szbergeron/yahp/sampler/src/sampler2.cpp

#include "config.cpp"
#include "utils.cpp"

#include "ADC.h"
#include "ADC_Module.h"
#include "core_pins.h"

#ifndef YAHP_SAMPLER
#define YAHP_SAMPLER

// it seems that a typical conversion takes about 4.92-ish
// microseconds when set to averaging(0) and the fastest
// conversion speed
//
// this gives us ~29000 cycles at stock clocks,
// which should give us some good compute during idle!
// it also means we get about 49 microseconds per
// sample of even a 20 key range (if we aren't split
// across boards weirdly, and can run both adcs at
// full saturation), meaning 20 samples per millisecond
// of even a "pretty severe" load scenario across
// all "READY" keys therein
static const uint32_t CONVERSION_TIME_NS = 49000;

__attribute__((always_inline)) static inline void step_idle(uint32_t window_ns,
                                                            bool run_all);

struct sample_t {

  float height;
  uint32_t time;

  sample_t(float height, uint32_t time) : height(height), time(time) {}

  sample_t() : height(0), time(0) {}
};

template <uint32_t BUFSIZE = SAMPLE_BUFFER_LENGTH> struct sample_buf_t {
  sample_t buffer[BUFSIZE];

  // begin points at the newest sample,
  // and (begin + 1) % SAMPLE_BUFFER_LENGTH is the next newest
  uint32_t begin = 0;
  uint32_t size = 0;

  uint32_t unackd = 0;

  sample_buf_t() : begin(0), size(0), unackd(0) {}

  void add_sample(sample_t sample) {
    /*this->begin =
        (this->begin + SAMPLE_BUFFER_LENGTH - 1) % SAMPLE_BUFFER_LENGTH;*/
    this->begin++;
    this->begin %= BUFSIZE;

    this->unackd += 1;

    this->buffer[this->begin] = sample;
    if (this->size < BUFSIZE) {
      this->size++;
    }
  }

  void clear() {
    this->begin = 0;
    this->size = 0;
    this->unackd = 0;
  }

  // if n is greater than buffer length,
  // then the oldest still held sample is returned
  // if no samples exist, the sample will be "zero"
  sample_t read_nth_oldest(uint32_t n) {
    // Serial.println("N is: " + String(n));
    //  clamp n
    if (n > BUFSIZE) [[unlikely]] {
      n = BUFSIZE;
    }

    auto res = sample_t{0, 0};
    if (this->size == 0) {
      // keep default
    } else {
      auto start = this->begin;
      auto with_room = start + BUFSIZE;
      auto offsetted = with_room - n;
      auto idx = offsetted % BUFSIZE;
      // Serial.println("Returns idx: " + String(idx));
      res = this->buffer[idx];
    }

    return res;
  }

  inline sample_t latest() { return this->read_nth_oldest(0); }
};

struct sensor_t;

struct sample_request_t {
  sensor_t *sensor;
  uint8_t pin;

  sample_request_t() : sensor(nullptr), pin(0) {}

  // if this was default constructed, this will return false
  bool is_real() { return this->sensor != nullptr; }

  sample_request_t(uint8_t pin, sensor_t *sensor) : sensor(sensor), pin(pin) {}
};

struct sensor_t {
  enum class sensor_mode_e {
    KEY,
    PEDAL,
    FADER,
  };

  enum class poll_priority_e {
    SLOW, // the slowest of the bunch, means
          // we can poll "rarely" in computer timescales
          // indicates events that want to happen within
          // "window of present" at human timescales,
          // but is not
    RELAXED,
    CRITICAL,
  };

  uint32_t sensor_id = 0;

  sample_buf_t<SAMPLE_BUFFER_LENGTH> buf;
  poll_priority_e priority = poll_priority_e::RELAXED;
  interpolater_t<MAGNET_INTERPOLATOR_POINTS> curve;

  uint8_t pin = 0;

  // key should be immediately sampled
  bool due_now() {
    uint32_t now = micros();

    switch (this->priority) {
    case poll_priority_e::SLOW:
      // TODO
      return true;
    case poll_priority_e::RELAXED:
      if (now - this->buf.latest().time > MAX_STALENESS_MICROS) {
        return true;
      } else {
        return false;
      }
    case poll_priority_e::CRITICAL:
      return true; // AFAP, but why are you asking me?
    default:
      [[unlikely]] return false;
    }
  }

  // key should be sampled _if convenient_
  bool due_relaxed() {
    uint32_t now = micros();

    if (now - this->buf.latest().time > MIN_STALENESS_MICROS) {
      return true;
    } else {
      return false;
    }
  }

  sample_request_t make_sample_request() {
    return sample_request_t(this->pin, this);
  }

  void add_raw_sample(uint32_t time, uint16_t raw_value) {
    auto nv = this->curve.interpolate(raw_value);
    this->buf.add_sample(sample_t(nv, time));
  }

  sensor_t(uint8_t pin, uint32_t sensor_id,
           vector_t<point_t, MAGNET_INTERPOLATOR_POINTS> curve)
      : sensor_id(sensor_id), curve(curve), pin(pin) {
    //
  }

  /*sensor_t(): curve(0, 1000) {
    // errorln("sensor_t was default constructed");
  }*/
};

struct adc_info_t {
  bool allowed_pins[PIN_COUNT];
  ADC_Module *adcm;

  adc_info_t(int idx, ADC *adc)
      : allowed_pins{}, adcm(idx == 0 ? adc->adc0 : adc->adc1) {
    for (int i = 0; i < KEYS_PER_BOARD; i++) {
      auto pin = pins[i];
      auto allowed = adcm->checkPin(pin);
      this->allowed_pins[pin] = allowed;
    }
  }

  adc_info_t() : allowed_pins{}, adcm(nullptr) {}
};

struct adcs_info_t {
  ADC *adcp;
  adc_info_t adc[2];

  adcs_info_t(ADC *adcp)
      : adcp(adcp), adc{adc_info_t(0, adcp), adc_info_t(1, adcp)} {}

  adcs_info_t() : adc{} {}
};

struct board_t {
  vector_t<sensor_t, KEYS_PER_BOARD> keys;
  uint8_t board_num;
  adcs_info_t adcs;

  void do_round() {
    // check if we even need to sample anything
    bool some_due = false;

    for (auto &k : this->keys) {
      if (k.due_now()) {
        some_due = true;
      }
    }

    if (!some_due) {
      // move on asap
      return;
    } else {
      // set board now so we have time for sample
      set_board(this->board_num);
      delayMicroseconds(1);
    }

    // start setting the pins _now_
    // so we have as much time as possible
    // before needing to sample

    vector_t<sample_request_t, KEYS_PER_BOARD> requests;

    for (auto &k : this->keys) {
      if (k.due_now() || k.due_relaxed()) {
        auto r = k.make_sample_request();
        requests.push_back(r);
      }
    }

    this->sample_all(requests);
  }

  void sample_all(vector_t<sample_request_t, KEYS_PER_BOARD> &requests) {
    vector_t<sample_request_t, KEYS_PER_BOARD> for_a;
    vector_t<sample_request_t, KEYS_PER_BOARD> for_b;
    vector_t<sample_request_t, KEYS_PER_BOARD> for_both;

    for (auto request : requests) {
      bool allowed_0i = this->adcs.adc[0].allowed_pins[request.pin];
      bool allowed_1i = this->adcs.adc[1].allowed_pins[request.pin];

      if (allowed_0i && allowed_1i) {
        // allowed for both, can't yet assign greedily
        for_both.push_back(request);
      } else if (allowed_0i) {
        // exclusively allowed for adc0, so can greedily push
        for_a.push_back(request);
      } else if (allowed_1i) {
        // same for adc1
        for_b.push_back(request);
      } else {
        // ???
        errorln("an assigned pin wasn't valid on either adc for sampling");
      }
    }

    sample_request_t a;
    sample_request_t b;

    while (!for_a.empty() || !for_b.empty() || !for_both.empty()) {
      if (!for_a.empty()) {
        a = for_a.pop_back().unwrap();
      } else if (!for_both.empty()) {
        a = for_both.pop_back().unwrap();
      }

      if (!for_b.empty()) {
        b = for_b.pop_back().unwrap();
      } else if (!for_both.empty()) {
        b = for_both.pop_back().unwrap();
      }

      uint32_t ts_a;
      uint32_t ts_b;

      auto &adc_a = this->adcs.adc[0].adcm;
      auto &adc_b = this->adcs.adc[1].adcm;

#undef FASTREAD
#ifdef FASTREAD
      if (a.is_real()) {
#ifdef YAHP_DEBUG
        bool v = adc_a->checkPin(a.pin);
        if (!v) {
          eloop(String("adc 0 (a) tried to read disallowed pin: ") + a.pin);
        }
#endif
        adc_a->startReadFast(a.pin);
        ts_a = micros();
        ;
      }

      if (b.is_real()) {
#ifdef YAHP_DEBUG
        bool v = adc_b->checkPin(b.pin);
        if (!v) {
          eloop(String("adc 1 (b) tried to read disallowed pin: ") + b.pin);
        }
#endif
        adc_b->startReadFast(b.pin);
        ts_b = micros();
        ;
      }

      // do one big-budget run
      step_idle(CONVERSION_TIME_NS, false);

      while (true) {
        bool a_done = true;
        bool b_done = true;

        // is either one done?
        if (a.is_real() && !adc_a->isComplete()) {
          a_done = false;
        }
        if (b.is_real() && !adc_b->isComplete()) {
          b_done = false;
        }

        // track when _both_ are complete
        // so that we avoid having to do individual stalls below,
        // should reduce code size in this loop
        if (a_done && b_done) {
          break;
        }

        // if not, at the moment we want to avoid
        // too much complexity and the gains from calling
        // step_once _again_ with so little time remaining
        // would probably be negligible
      }

      // get values
      if (a.is_real()) {
        auto v_a = adc_a->readSingle();
        sample_t s(v_a, ts_a);
        a.sensor->add_sample(s);
      }

      if (b.is_real()) {
        auto v_b = adc_b->readSingle();
        sample_t s(v_b, ts_b);
        a.sensor->add_sample(s);
      }
#elif defined(FASTREAD2)
      //
#else
      // Serial.println("Adding round");
      if (a.is_real() && b.is_real()) {
        ts_a = micros();
        ts_b = micros();

        auto r = this->adcs.adcp->analogSynchronizedRead(a.pin, b.pin);
        auto v_a = r.result_adc0;
        auto v_b = r.result_adc1;
        /*adc_a->startSingleRead(a.pin);
        adc_b->startSingleRead(b.pin);

        step_idle(CONVERSION_TIME_NS, false);

        auto v_a = adc_a->readSingle();
        auto v_b = adc_b->readSingle();*/
        sample_t sa(v_a, ts_a);
        sample_t sb(v_b, ts_b);

        a.sensor->add_raw_sample(ts_a, v_a);
        b.sensor->add_raw_sample(ts_b, v_b);

      } else if (a.is_real()) {

        ts_a = micros();
        auto v_a = adc_a->analogRead(a.pin);

        a.sensor->add_raw_sample(ts_a, v_a);

      } else if (b.is_real()) {

        ts_b = micros();
        auto v_b = adc_b->analogRead(b.pin);

        b.sensor->add_raw_sample(ts_b, v_b);
      }

#endif
    }
  }

  board_t(boardspec_t &bspec, adcs_info_t &adcs_info)
      : board_num(bspec.board_num), adcs(adcs_info) {
    for (auto &keyc : bspec.sensors) {
      Serial.printf("Creates sensor by id %d\r\n", keyc.sensor_id);
      sensor_t sensor(keyc.pin_num, keyc.sensor_id, keyc.curve);
      this->keys.push_back(sensor);
    }
  }
};

struct sampler_t {
  ADC *adc = nullptr;
  vector_t<board_t, NUM_BOARDS> boards;

  sensor_t *find_sensor(uint32_t sensor_id) {
    for (auto &board : this->boards) {
      for (auto &sensor : board.keys) {
        if (sensor.sensor_id == sensor_id) {
          return &sensor;
        }
      }
    }
    Serial.printf("Unable to find sensor by id %d?\r\n", sensor_id);
    for (auto &board : this->boards) {
      Serial.printf("Board by id %d:\r\n", (int)board.board_num);
      for (auto &sensor : board.keys) {
        Serial.printf("    Sensor by id %d\r\n", sensor.sensor_id);
      }
    }

    return nullptr;
  }

  sampler_t(ADC adc_, samplerspec_t &spec) : adc(new ADC(adc_)) {
    for (auto boardc : spec.boards) {
      adcs_info_t info(this->adc);
      Serial.printf("Makes board: %d\r\n", (int)boardc.board_num);
      board_t b(boardc, info);
      this->boards.push_back(b);
    }
  }

  ~sampler_t() { delete this->adc; }

  void sample_round() {
    set_board_pins();
    delayMicroseconds(10);
    for (auto &board : this->boards) {
      board.do_round();
    }
  }
};

#endif
