szbergeron/yahp/sampler/src/calibrate.cpp

#include "avr/pgmspace.h"
#include "config.cpp"
#include "key.cpp"
#include "keyboard.cpp"
#include "magnets.cpp"
#include "pins_arduino.h"
#include "usb_serial.h"
#include "utils.cpp"

#include "ArduinoJson/Document/JsonDocument.hpp"
#include "ArduinoJson/Object/JsonObject.hpp"

#include "core_pins.h"
#include "elapsedMillis.h"
#include <cstddef>
#include <cstdint>
#include <ostream>

#ifndef YAHP_CALIBRATE
#define YAHP_CALIBRATE
void blinkblink() {
  for (int i = 0; i < 3; i++) {
    digitalWrite(LED_BUILTIN, 1);
    delay(150);
    digitalWrite(LED_BUILTIN, 0);
    delay(250);
  }
}

void testmode(tempboards_t &boards) {
  while (true) {
    Serial.println("1) fast toggle with numeric output");
    Serial.println("2) toggle board on enter");
    auto num = prompt_int("make choice:", 1, 3, 0);
    if (num == 1) {
      while (!newline_waiting()) {
        for (auto &board : boards.boards) {
          Serial.printf("\r\nSetting to board %d\r\n", (uint32_t)board);
          set_board(board);
          delayMicroseconds(50);

          for (uint32_t ipin = 0; ipin < KEYS_PER_BOARD; ipin++) {
            uint32_t val = analogRead(pins[ipin]);
            Serial.printf("%04d ", val);
          }
          Serial.printf("\r\n");
        }

        delay(100);
      }
    } else if (num == 2) {
      while (true) {
        for (auto &board : boards.boards) {
          Serial.printf("\r\nSetting to board %d\r\n", (uint32_t)board);
          set_board(board);
          delayMicroseconds(50);

          while (!newline_waiting()) {
            for (uint32_t ipin = 0; ipin < KEYS_PER_BOARD; ipin++) {
              uint32_t val = analogRead(pins[ipin]);
              Serial.printf("%04d ", val);
            }
            Serial.printf("\r");
          }
        }

        delay(100);
      }
    }
  }
}

tempboards_t detect_boards() {
  Serial.println("Getting board info");
  // const size_t LINE_LEN = 256;
  // uint8_t linebuf[LINE_LEN];

  // first, detect which boards are present
  // do this by checking if we can pull up/down
  // the voltage on the lines, or if
  // they automatically return to some given value
  // // for now, just ask \:)
  Serial.print("How many boards are there? [0-255]:");

  uint8_t board_count = prompt_int("How many boards are there?", 0, 255, 1);

  Serial.printf("Setting to %d boards\n\r", board_count);

  vector_t<uint8_t, NUM_BOARDS> boards;

  bool sequential = false;

  sequential =
      confirm("Are they numbered sequentially starting from zero?", true);

  Serial.println();

  if (sequential) {
    for (size_t i = 0; i < board_count; i++) {
      boards.push_back(i);
    }
  } else {
    for (size_t i = 0; i < board_count; i++) {
      uint8_t bid = prompt_int(String("What is the board ID of board number ") +
                                   String(i) + "?",
                               0, 255, i);

      boards.push_back(bid);
    }
  }

  return {boards};
}

vector_t<vector_t<bool, KEYS_PER_BOARD>, NUM_BOARDS>
detect_keys(tempboards_t &boards) {

  for (size_t i = 0; i < KEYS_PER_BOARD; i++) {
    pinMode(pins[i], INPUT_PULLDOWN);
  }

  analogReadResolution(10);

  analogReadAveraging(16);

  Serial.println("Detecting keys on boards, using voltage threshold of 0.1v as "
                 "'grounded'");

  float vp = 0.1 / 3.3;
  float thres_f = vp * 1024;
  uint32_t thres = thres_f;

  vector_t<vector_t<bool, KEYS_PER_BOARD>, NUM_BOARDS> info;

  for (auto &bid : boards.boards) {
    set_board(bid);
    delayMicroseconds(100);

    vector_t<bool, KEYS_PER_BOARD> bi;

    for (size_t i = 0; i < KEYS_PER_BOARD; i++) {
      delayMicroseconds(30);
      uint32_t val = analogRead(pins[i]);

      if (val > thres) {
        bi.push_back(true);
      } else {
        bi.push_back(false);
      }
    }

    info.push_back(bi);
  }

  Serial.println("Discovered sensor configuration:");

  for (size_t b = 0; b < info.size(); b++) {
    auto &bd = info[b];

    Serial.printf("  (%d)[", b);

    for (size_t s = 0; s < bd.size(); s++) {
      auto present = bd[s];

      if (present) {
        Serial.print("X");
      } else {
        Serial.print("_");
      }
    }

    Serial.print("]");
  }

  for (size_t b = 0; b < info.size(); b++) {
    Serial.printf("b# %d has %d\r\n", b, info[b].size());
  }

  Serial.println();

  return info;
}

float gather_gbl_val(String msg, key_calibration_t &kc, sensorspec_t &ssp) {
  Serial.println(msg);
  Serial.println();
  float latest = 0;
  while (true) {
    if (newline_waiting()) {
      break;
    }

    auto v = analogRead(ssp.pin_num);
    float normal = kc.map(v);

    Serial.print("\r");
    for (int i = 0; i < 12; i++) {
      Serial.print("          ");
    }
    Serial.print("\r");
    print_normalized(normal);
    latest = normal;
    delay(30);
  }

  float val = prompt_float(msg, 0, 1, latest);
  Serial.printf("You selected %f\r\n", val);
  bool c = confirm("do you want to continue with this val?", true);
  if (c) {
    return val;
  } else {
    return gather_gbl_val(msg, kc, ssp);
  }
}

global_key_config_t gbl_config(keyboardspec_t &spec) {
  Serial.println("making global");
  sensorspec_t *sensor = nullptr;
  boardspec_t *board = nullptr;
  key_spec_t *key = nullptr;
  // just pick a key
  for (auto &board_i : spec.sampler.boards) {
    board = &board_i;
    for (auto &sensor_i : board_i.sensors) {
      sensor = &sensor_i;
      goto OUT;
    }
  }
OUT:

  if (sensor == nullptr) {
    Serial.println("No keys were found!");
    return global_key_config_t();
  }

  for (auto &key_i : spec.keys) {
    if (key_i.sensor_id == sensor->sensor_id) {
      key = &key_i;
    }
  }

  if (key == nullptr) {
    Serial.println("No keys were found!");
    return global_key_config_t();
  }

  // now, figure out detect range
  auto kc = key_calibration_t(*key, *sensor);

  set_board(board->board_num);
  delay(3);

  global_key_config_t gbl;

  gbl.strike =
      gather_gbl_val("What strike point do you want to use?", kc, *sensor);
  gbl.letoff =
      gather_gbl_val("What letoff point do you want to use?", kc, *sensor);
  gbl.repetition =
      gather_gbl_val("What repetition point do you want to use?", kc, *sensor);
  gbl.active =
      gather_gbl_val("What active point do you want to use?", kc, *sensor);
  gbl.damper_down =
      gather_gbl_val("What damper_down point do you want to use?", kc, *sensor);
  gbl.damper_up =
      gather_gbl_val("What damper_up point do you want to use?", kc, *sensor);

  return gbl;
}

tempkey_t select_key(tempboards_t &boards) {
  analogReadResolution(10);
  analogReadAveraging(16);

  uint32_t baselines[NUM_BOARDS][KEYS_PER_BOARD];
  for (size_t b = 0; b < NUM_BOARDS; b++) {
    for (size_t k = 0; k < KEYS_PER_BOARD; k++) {
      baselines[b][k] = 0x9FFF;
    }
  }

  delayMicroseconds(100);

  for (size_t b = 0; b < boards.boards.size(); b++) {
    auto bnum = boards.boards[b];
    set_board(bnum);
    delayMicroseconds(100);

    for (size_t knum = 0; knum < KEYS_PER_BOARD; knum++) {
      auto pin = pins[knum];
      baselines[b][knum] = analogRead(pin);
    }
  }

  Serial.println("Please press the key you want to select");

  while (true) {
    for (size_t b = 0; b < boards.boards.size(); b++) {
      auto bnum = boards.boards[b];
      set_board(bnum);
      delayMicroseconds(100);

      for (size_t knum = 0; knum < KEYS_PER_BOARD; knum++) {
        auto pin = pins[knum];
        uint32_t baseline = baselines[b][knum];
        uint16_t val = analogRead(pin);
        if (val > baseline + 75) {
          for (int i = 0; i < 16; i++) {
            if ((uint32_t)analogRead(pin) < baseline + 75) {
              Serial.printf("had a spurious spike, static?");
              goto OUT;
            }
          }
          Serial.printf("baseline was %d, val found was %d, on bnum %d pin %d, "
                        "pin_index %d\r\n",
                        (int)baseline, (int)val, (int)bnum, (int)pin,
                        (int)knum);
          return tempkey_t(bnum, pin);
        }
      OUT:
        continue;
      }
    }
  }
}

void testmode_entry() {
  auto boards = detect_boards();
  testmode(boards);
}

keyboardspec_t key_calibration2() {
    while (!newline_waiting()) {
      delay(500);
      Serial.println("Press enter to continue");
    }

    auto boards = detect_boards();

    uint32_t start_midi =
        prompt_int("What is the lowest midi note on your piano? (Usually the "
                   "minimum on an 88 key keyboard is 21)",
                   0, 127, FIRST_MIDI_NOTE + 30);
        uint32_t midi_channel = prompt_int(
            "What midi channel should notes play on by default?", 0, 16, 1);

    Serial.printf("Please play each key, one at a time, ascending from 0");
    Serial.printf("When done, hit enter");

    vector_t<tempkey_t, KEY_COUNT_MAX> ided_sensors;

    vector_t<key_spec_t, KEY_COUNT_MAX> kspecs;
    vector_t<boardspec_t, KEY_COUNT_MAX> bspecs;

    size_t sensor_id = 0;

    while(!newline_waiting()) {
        auto k = select_key(boards);
        if(ided_sensors.contains(k)) {
            continue;
        }

        ided_sensors.push_back(k);

        auto sid = sensor_id++;
        auto mnid = start_midi++;
        sensorspec_t(sid, k.pin, {});
        key_spec_t(sid, mnid, midi_channel);

        auto bn = k.board;

        auto b = bspecs.find_by_or_insert([bn](const boardspec_t &b) { return bn == b.board_num; }, boardspec_t());

    }

}

void more_calibration(fullspec_t fspec) {
}

keyboardspec_t key_calibration() {
  while (!newline_waiting()) {
    delay(500);
    Serial.println("Press enter to continue");
  }

  auto boards = detect_boards();

  if (confirm("enter test mode?", false)) {
    testmode(boards);
  }

  bool fastcal = confirm("Do you want to use fastcal?", true);

  samplerspec_t samplerspec;
  vector_t<key_spec_t, KEY_COUNT_MAX> keys;
  vector_t<pedal_spec_t, PEDAL_COUNT_MAX> pedals;

  uint32_t start_midi =
      prompt_int("What is the lowest midi note on your piano? (Usually the "
                 "minimum on an 88 key keyboard is 21)",
                 0, 127, FIRST_MIDI_NOTE + 30);

  uint32_t midi_channel = prompt_int(
      "What midi channel should notes play on by default?", 0, 16, 1);

  uint32_t num_keys =
      prompt_int("How many keys does your piano have?", 0, 127 - start_midi,
                 min(88, 127 - (int32_t)start_midi));

  uint32_t csid = 0;
  for (uint32_t midi_num = start_midi; midi_num < start_midi + num_keys;
       midi_num++) {
    auto n = format_note(midi_num);
    Serial.printf("Configuring note %s (midi id %d)\r\n", n.c_str(),
                  (int)midi_num);
    bool in_use = fastcal || confirm("Configure this key?", true);
    if (!in_use) {
      continue;
    }

    Serial.printf("Please press %s on your piano (will be sid %d)\r\n",
                  n.c_str(), csid);
    auto sensor = select_key(boards);

    //

    Serial.printf("Key %s is assigned pin %d on board %d\r\n", n.c_str(),
                  (int)sensor.pin, (int)sensor.board);

    auto interpolater = drop_test(sensor.board, sensor.pin, fastcal);

    uint32_t sid = csid++;

    sensorspec_t sensorspec(sid, sensor.pin, interpolater.points);

    samplerspec.get_board(sensor.board).sensors.push_back(sensorspec);
    key_spec_t k(sid, midi_num, midi_channel);
    keys.push_back(k);
  }

  while (confirm("Do you have an additional pedal to add?", false)) {
    Serial.println("Not implemented");
  }

  return keyboardspec_t(samplerspec, keys, pedals);
}

float read_key(uint32_t sid, keyboard_t *kbd) {
  return kbd->sampler->find_sensor(sid)->buf.latest().height;
}

// Doesn't free itself, reboot after done!
keyboard_t *make_kbd(fullspec_t spec) {
  ADC adc;
  auto sampler = new sampler_t(adc, spec.keyboard.sampler);
  auto kbd = new keyboard_t(spec, sampler);

  return kbd;
}

JsonDocument configure_offsets(fullspec_t &spec) {
  auto kbd = make_kbd(spec);

  confirm("Hands off the keyboard! Hit enter once understood", true);
  delay(500);

  const uint32_t AVERAGES_COUNT = 500;

  for (uint32_t averages = 0; averages < AVERAGES_COUNT; averages++) {
    /*for (auto &key : spec.keyboard.keys) {
        //
    }*/
    //
    kbd->sampler->sample_round();
    for (kbd_key_t &key : kbd->keys) {
      float cur_val = read_key(key.sensor->sensor_id, kbd);

      if (averages == 0) {
        key.calibration.spec.bound_min = cur_val;
        key.calibration.spec.bound_max = cur_val;
      } else {
        key.calibration.spec.bound_min =
            (key.calibration.spec.bound_min * averages + cur_val) /
            (averages + 1);
      }
    }
  }

  Serial.println("Now, play each note at PPP level (or lift the hammer just "
                 "barely to touch the striker rail!)");
  Serial.println("Press enter when done");

  while (!newline_waiting()) {
    kbd->sampler->sample_round();
    for (kbd_key_t &key : kbd->keys) {
      float cur_val = read_key(key.sensor->sensor_id, kbd);

      key.calibration.spec.bound_max =
          max(key.calibration.spec.bound_max, cur_val);
    }
  }

  if (confirm("Do you want to use the new range config generated here?",
              true)) {
    JsonDocument jd;
    for (kbd_key_t &key : kbd->keys) {
      JsonDocument jdi;

      jdi["min"] = key.calibration.spec.bound_min;
      jdi["max"] = key.calibration.spec.bound_max;

      jd[key.sensor->sensor_id] = jdi;
      //
    }

    return jd;
  } else {
    // just reboot
    doReboot();
    JsonDocument never;
    return never;
  }
}

const size_t JSON_FILE_MAX_LENGTH = 250000;
DMAMEM char JSON_FILE[JSON_FILE_MAX_LENGTH];

result_t<JsonDocument *, unit_t> json_from_sd(const char *name) {
  Serial.println("Grabbing json from sd");

  if (!SD.exists(name)) {
    Serial.println("No config on SD");
    return result_t<JsonDocument *, unit_t>::err({});
  }

  auto f = SD.open(name, FILE_READ);

  size_t file_size = 0;

  file_size = f.readBytes((char*)JSON_FILE, JSON_FILE_MAX_LENGTH);

  JSON_FILE[file_size] = 0; // null term

  f.close();

  Serial.println("done loading file");

  JsonDocument *doc = new JsonDocument;
  deserializeJson(*doc, (char*)JSON_FILE);

  Serial.println("deserialized");

  return result_t<JsonDocument *, unit_t>::ok(doc);
}

void json_to_sd(const char *name, JsonDocument doc) {
  Serial.println("Saving config to sd...");
  auto f = SD.open(name, FILE_WRITE_BEGIN);
  size_t len = serializeJsonPretty(doc, f);
  f.flush();
  f.close();
}

static fullspec_t get_spec() {
  keyboardspec_t s;
  {
    auto r = json_from_sd("calibration.json");
    if (r.is_ok()) {
      auto d = r.unwrap();
      Serial.println("Loaded calibration json file");
      // we already have sampler then
      s = keyboardspec_t((*d).as<JsonObject>());
      delete d;
    } else {
      s = key_calibration();
      json_to_sd("calibration.json", s.to_json());

      // come back through now
      // with a fresh heap, and sane everything
      doReboot();
    }
  }

  Serial.println("Loaded calibration data");

  global_key_config_t gbl;
  {
    auto r2 = json_from_sd("global.json");
    if (r2.is_ok()) {
      auto d = r2.unwrap();
      // return samplerspec_t(r.unwrap().as<JsonObject>());
      gbl = global_key_config_t((*d).as<JsonObject>());
      delete d;
    } else {
      gbl = gbl_config(s);
      json_to_sd("global.json", gbl.to_json());

      // fresh heap, uniform flow
      // (always want to return based on value of load)
      doReboot();
    }
  }

  auto spec = fullspec_t(s, gbl);

  {
    auto r = json_from_sd("offsets.json");
    if (r.is_ok()) {
      JsonDocument *d = r.unwrap();
      JsonObject o = (*d).as<JsonObject>();
      for (key_spec_t &key : spec.keyboard.keys) {
        if (o.containsKey(String(key.sensor_id))) {
          JsonObject ko = o[String(key.sensor_id)];
          key.bound_min = ko["min"];
          key.bound_max = ko["max"];
        }
      }
      delete d;
    } else {
      auto jd = configure_offsets(spec);
      json_to_sd("offsets.json", jd);
      doReboot();
    }
  }

  return spec;
}

#endif
